dycli/petrock/demo/06-bottom-angled.png

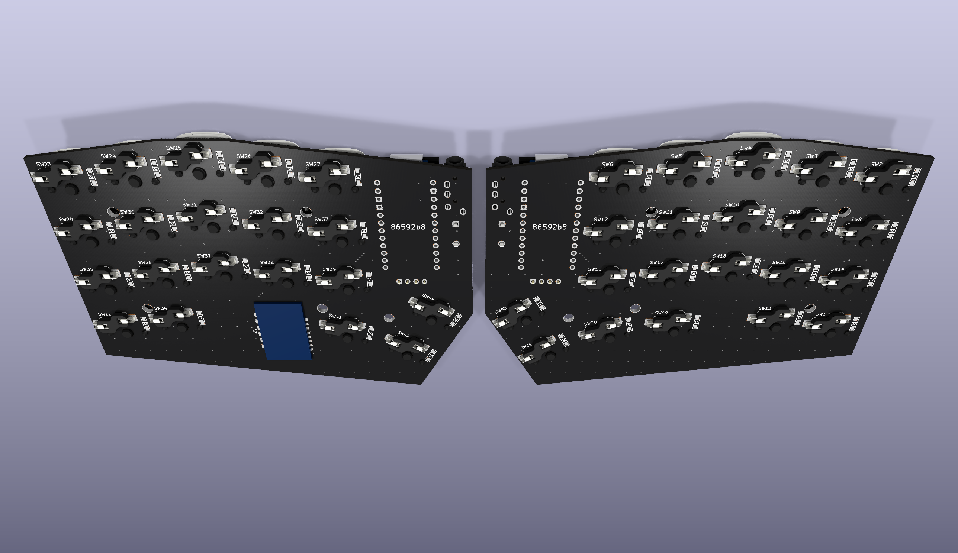
demo/06-bottom-angled.png
