dycli/petrock/demo/07-switch-plate.png

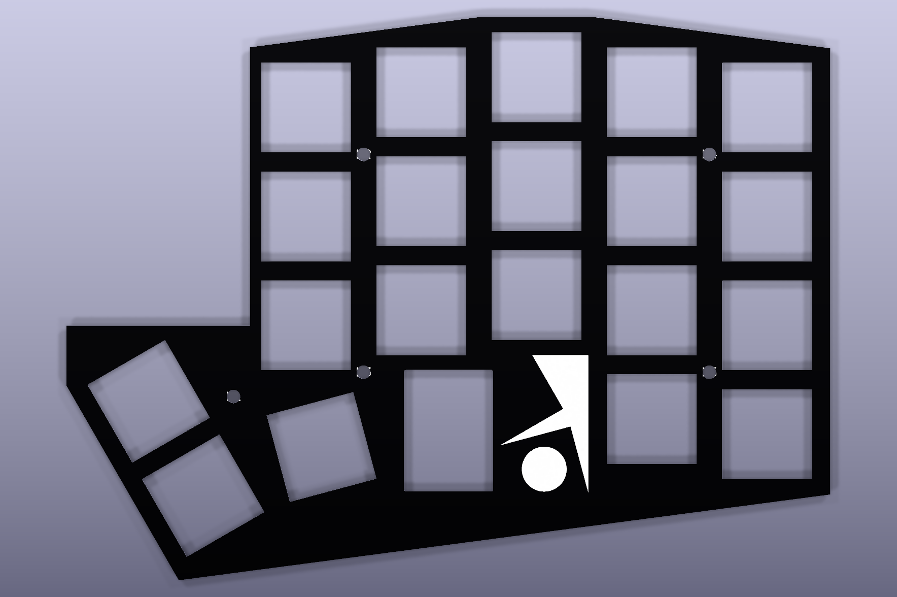
demo/07-switch-plate.png
