dycli/petrock/demo/09-left-thumbs-closeup.png

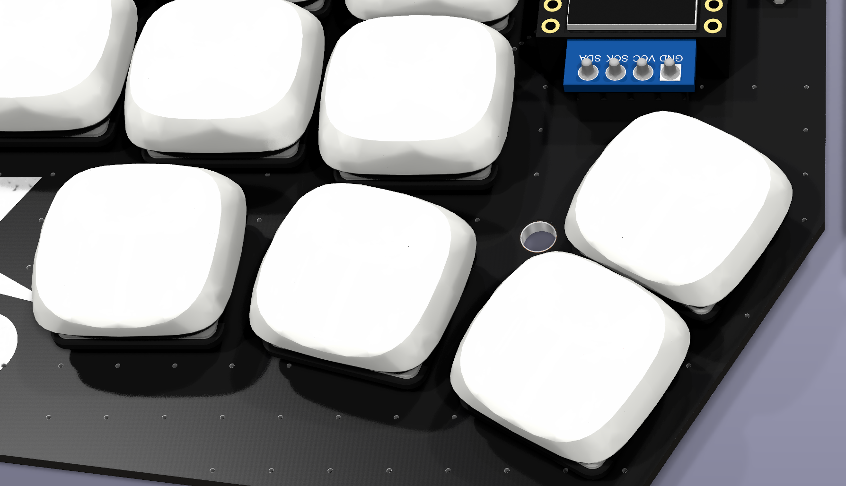
demo/09-left-thumbs-closeup.png
