dycli/petrock/demo/10-jacks-controllers-closeup.png

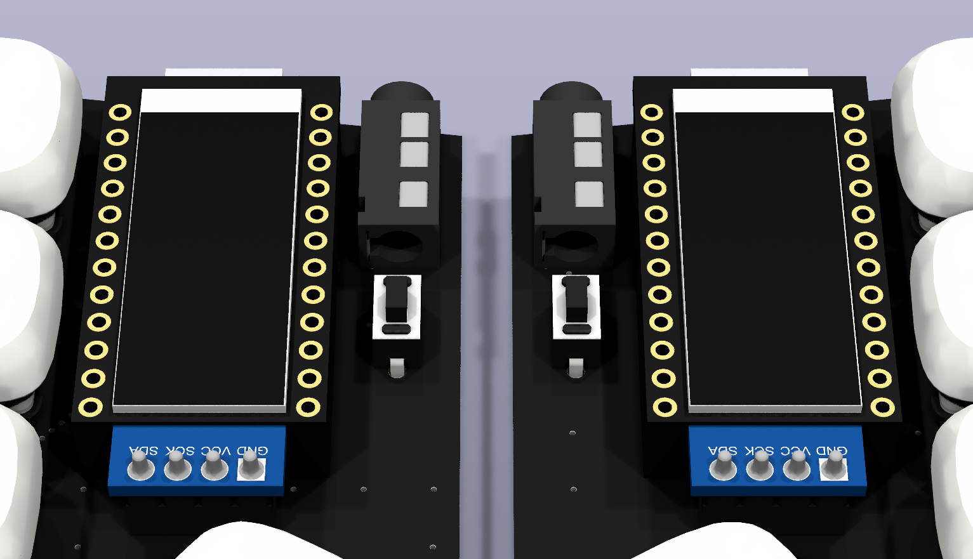
demo/10-jacks-controllers-closeup.png
