dycli/petrock/demo/11-before-after.png

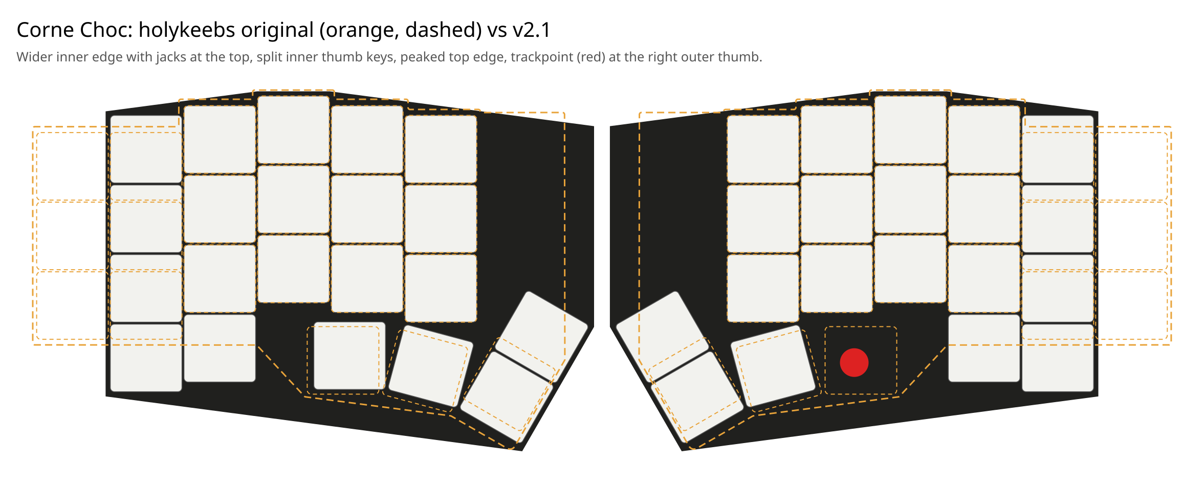
demo/11-before-after.png
