dycli/petrock/demo/petrock-40-copper-back.png

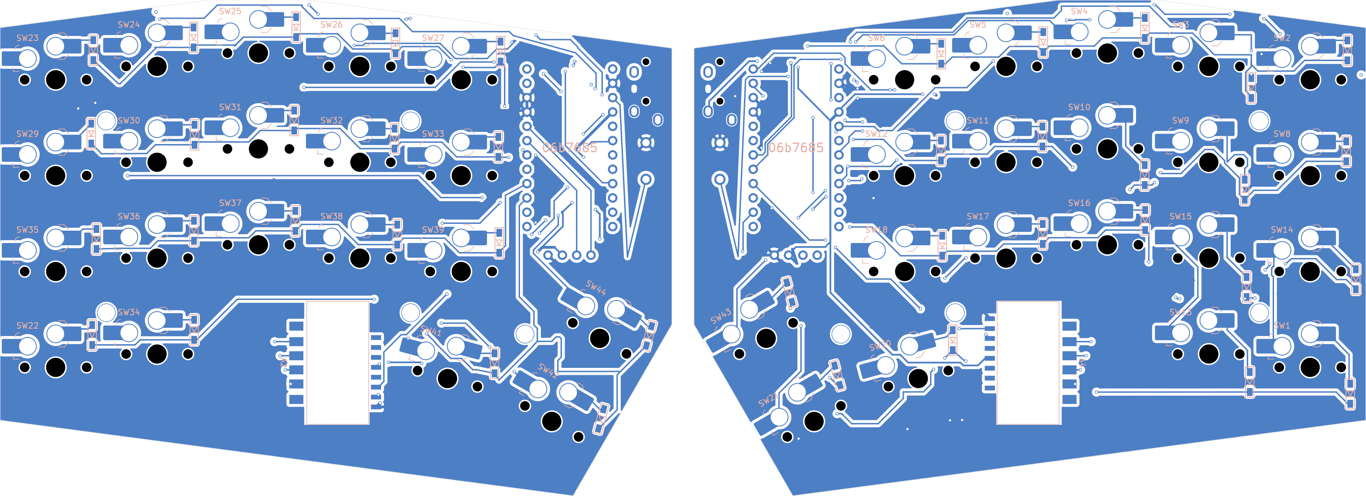
demo/petrock-40-copper-back.png
