dycli/petrock/demo/petrock-40-copper-front.png

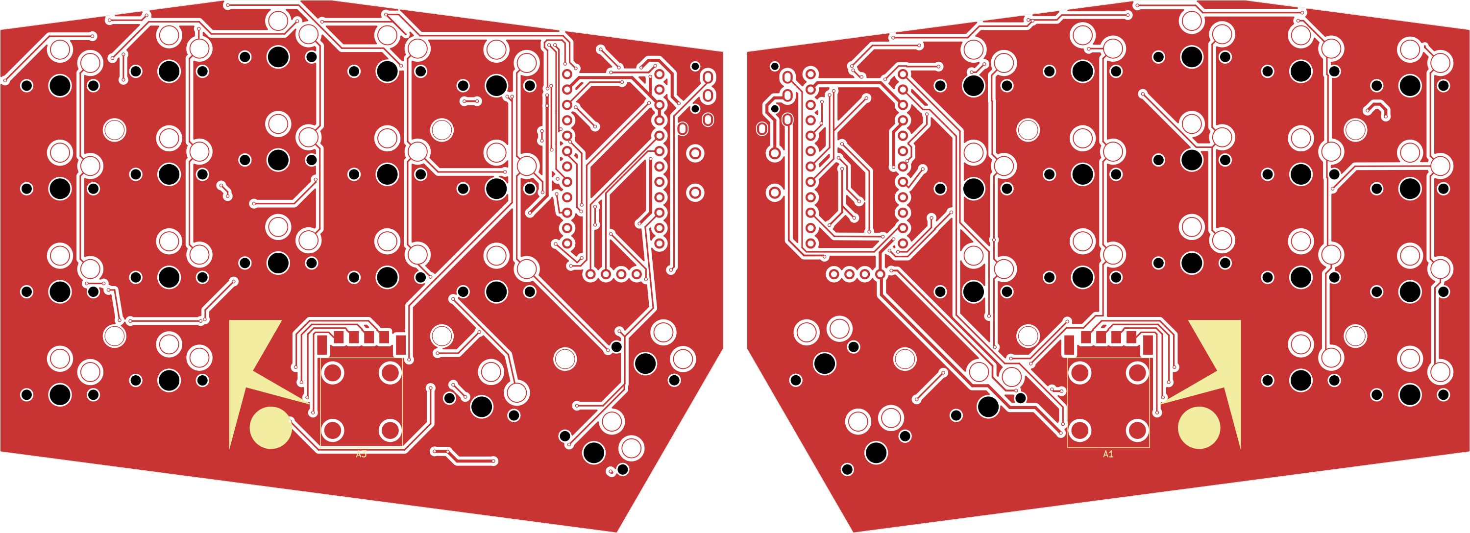
demo/petrock-40-copper-front.png
