dycli/petrock/demo/13-assembled-trackpoint.png

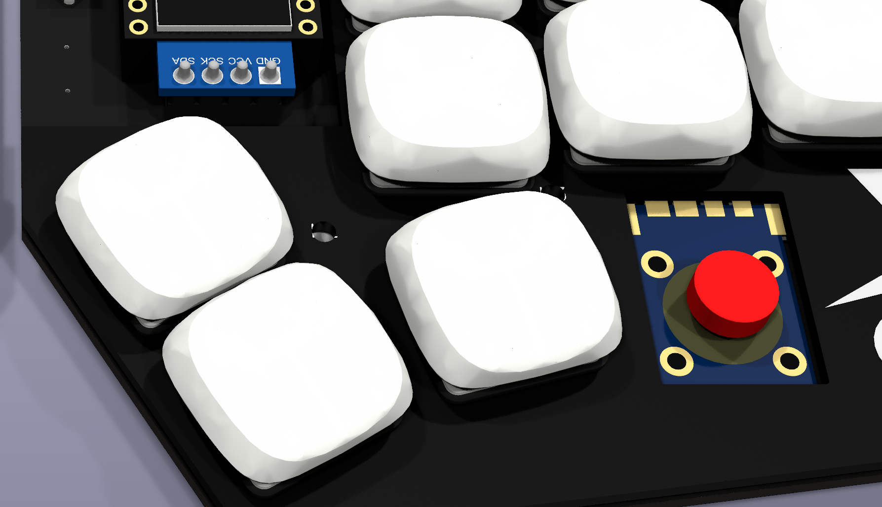
demo/13-assembled-trackpoint.png
